acha666/ADUMx165_USB_Isolator/ADUMx165_USB_Isolator.3dmodels/R_0402_1005Metric.step

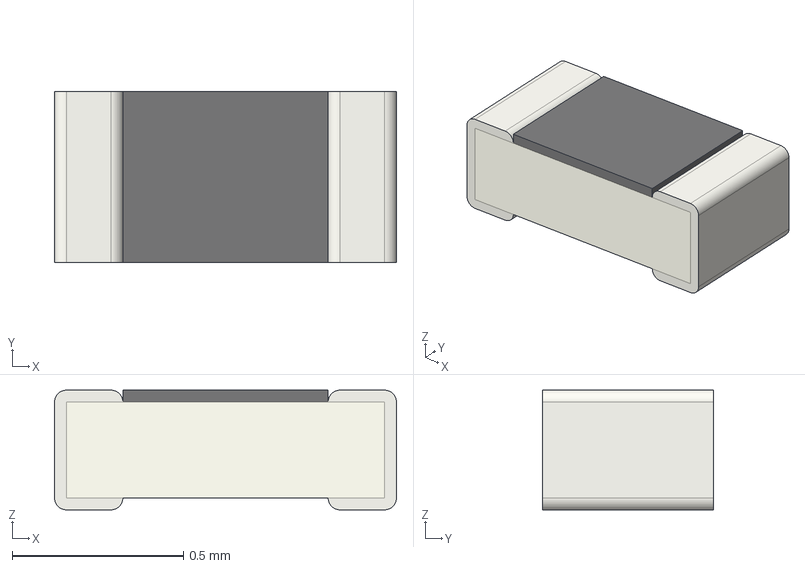
[picture p18: CAD file, 2024-11-15]
ADUMx165_USB_Isolator.3dmodels/R_0402_1005Metric.step
1.00 x 0.5 x 0.35 mm
