acha666/ADUMx165_USB_Isolator/ADUMx165_USB_Isolator.3dmodels/DRL0008A.stp

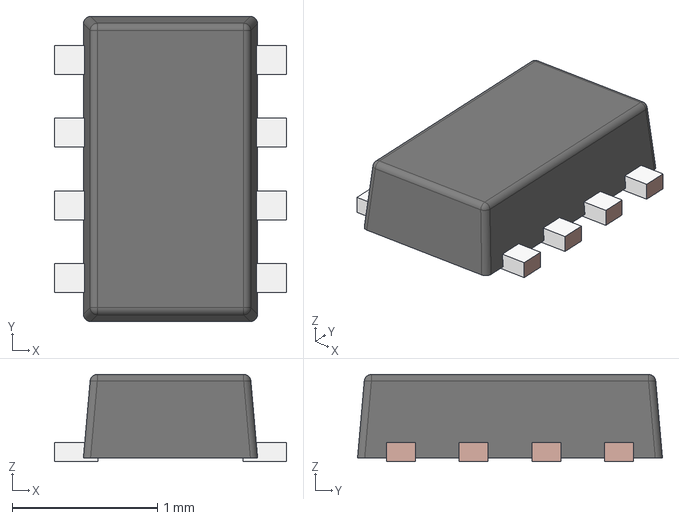
[picture p19: CAD file, 2024-11-13]
ADUMx165_USB_Isolator.3dmodels/DRL0008A.stp
1.60 x 2.10 x 0.6 mm
FRAME-DRL0008A
BODY-SOT
