acha666/ADUMx165_USB_Isolator/ADUMx165_USB_Isolator.3dmodels/Coilcraft-DA2303-AL.STEP

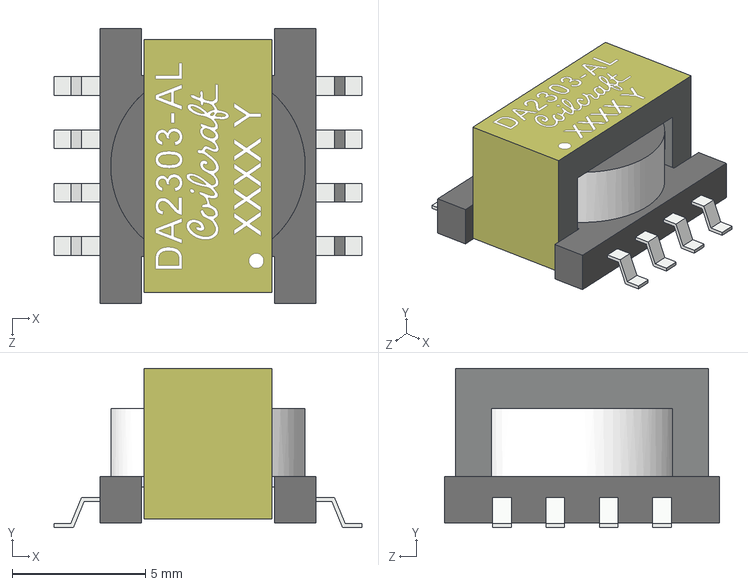
[picture p20: CAD file, 2024-11-13]
ADUMx165_USB_Isolator.3dmodels/Coilcraft-DA2303-AL.STEP
11.6 x 5.97 x 10.3 mm
