acha666/ADUMx165_USB_Isolator/ADUMx165_USB_Isolator.3dmodels/RUX0012A.stp

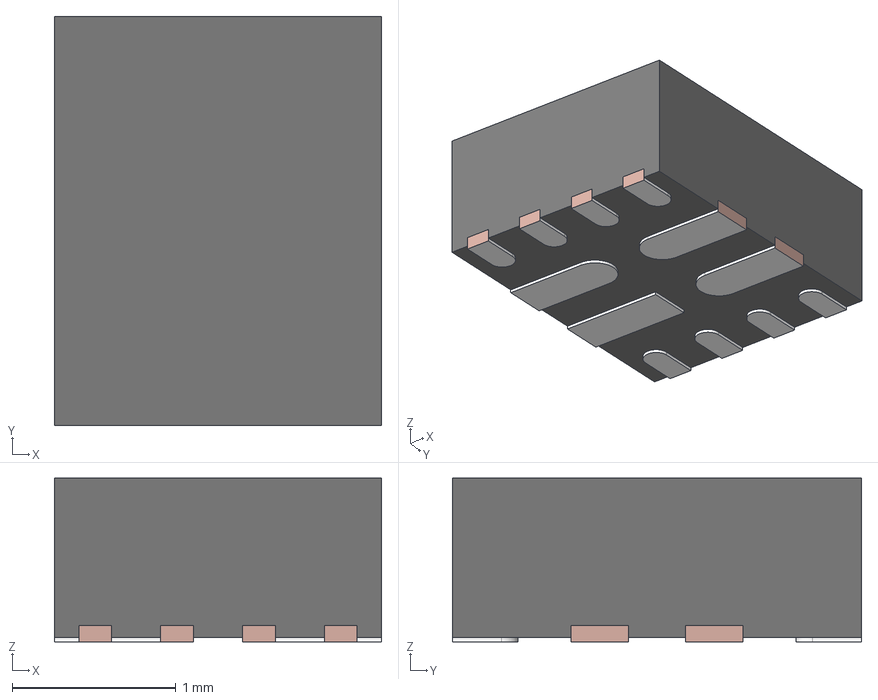
[picture p21: CAD file, 2024-11-13]
ADUMx165_USB_Isolator.3dmodels/RUX0012A.stp
2.00 x 2.50 x 1.00 mm
FRAME
MOLD
